olell/CoinMatrix/firmware/src/charlie.c

/**
 * matrix structure
 *
 *   0 1 2 3 4 ...
 * 0 x
 * 1   x
 * 2     x
 * 3       x
 * 4         x
 * ...
 */

#include "charlie.h"

#include "ch32fun.h"
#include "stdio.h"

// by "charlie_paramgen.py" precalculated values
#define CHARLIE_CYCLE_COUNT 192
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
    const uint_fast8_t out_val = charlie_out_vals[idx];

    const uint_fast8_t pwm = raw_pixels[idx];

    for (uint8_t tmp = 0; tmp < CHARLIE_MAX_BRIGHTNESS; tmp++) {
        *(out_reg) = (tmp < pwm) ? out_val : 0;
    }

    if (++idx == CHARLIE_CYCLE_COUNT) idx = 0;
}
