olell/CoinMatrix/firmware/include/gif.h

#ifndef _GIF_H
#define _GIF_H
#define GIF_LENGTH 1596
static const uint8_t GIF_INSTRUCTIONS[] = {0, 15, 255, 1, 15, 255, 2, 15, 255, 3, 15, 255, 4, 15, 255, 5, 15, 255, 6, 15, 255, 7, 15, 255, 8, 15, 255, 9, 15, 255, 10, 15, 255, 11, 15, 255, 12, 15, 255, 13, 15, 255, 15, 15, 255, 16, 15, 255, 17, 15, 255, 18, 15, 255, 19, 15, 255, 20, 15, 255, 21, 15, 255, 23, 15, 255, 24, 15, 255, 25, 15, 255, 27, 11, 187, 28, 15, 255, 29, 15, 255, 30, 15, 255, 31, 15, 255, 32, 15, 255, 33, 15, 255, 34, 15, 255, 35, 15, 255, 36, 15, 255, 37, 15, 255, 39, 15, 255, 40, 15, 255, 41, 15, 255, 42, 15, 96, 43, 15, 96, 44, 15, 255, 45, 0, 16, 46, 15, 255, 47, 15, 255, 48, 15, 255, 49, 15, 255, 50, 15, 255, 51, 3, 51, 52, 3, 51, 53, 15, 96, 54, 15, 255, 55, 15, 255, 56, 15, 255, 57, 15, 255, 58, 15, 255, 59, 15, 255, 60, 15, 255, 61, 15, 255, 62, 15, 255, 255, 15, 255, 0, 0, 0, 1, 0, 0, 2, 0, 0, 3, 0, 0, 4, 0, 0, 5, 7, 119, 6, 3, 51, 7, 0, 0, 8, 0, 0, 9, 0, 0, 10, 0, 0, 11, 0, 0, 12, 9, 153, 13, 10, 168, 14, 6, 102, 15, 0, 0, 16, 0, 0, 17, 0, 0, 18, 6, 102, 19, 10, 170, 20, 14, 238, 21, 14, 237, 22, 7, 118, 23, 0, 0, 24, 0, 0, 25, 0, 0, 26, 9, 153, 27, 14, 255, 30, 10, 170, 31, 0, 0, 32, 0, 0, 33, 0, 0, 34, 6, 84, 35, 14, 220, 37, 15, 255, 38, 6, 102, 39, 0, 0, 40, 0, 0, 41, 3, 0, 42, 10, 64, 43, 10, 81, 44, 10, 170, 45, 8, 118, 46, 0, 0, 47, 0, 0, 48, 0, 0, 49, 0, 0, 50, 4, 49, 51, 3, 34, 52, 2, 34, 53, 4, 16, 54, 1, 17, 55, 0, 0, 56, 0, 0, 57, 0, 0, 58, 2, 52, 59, 2, 51, 60, 0, 0, 61, 0, 0, 62, 0, 0, 255, 0, 0, 4, 1, 17, 5, 7, 119, 6, 1, 19, 12, 10,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
53, 27, 15, 255, 29, 13, 221, 30, 1, 17, 34, 8, 136, 37, 12, 221, 38, 1, 34, 42, 7, 48, 43, 9, 135, 44, 9, 153, 45, 6, 84, 46, 0, 0, 50, 3, 50, 51, 2, 34, 52, 2, 33, 53, 6, 32, 54, 2, 0, 58, 0, 54, 59, 0, 119, 60, 2, 37, 253, 0, 0};
#endif //_GIF_H
